svirant/DonutDongle/images/11.png

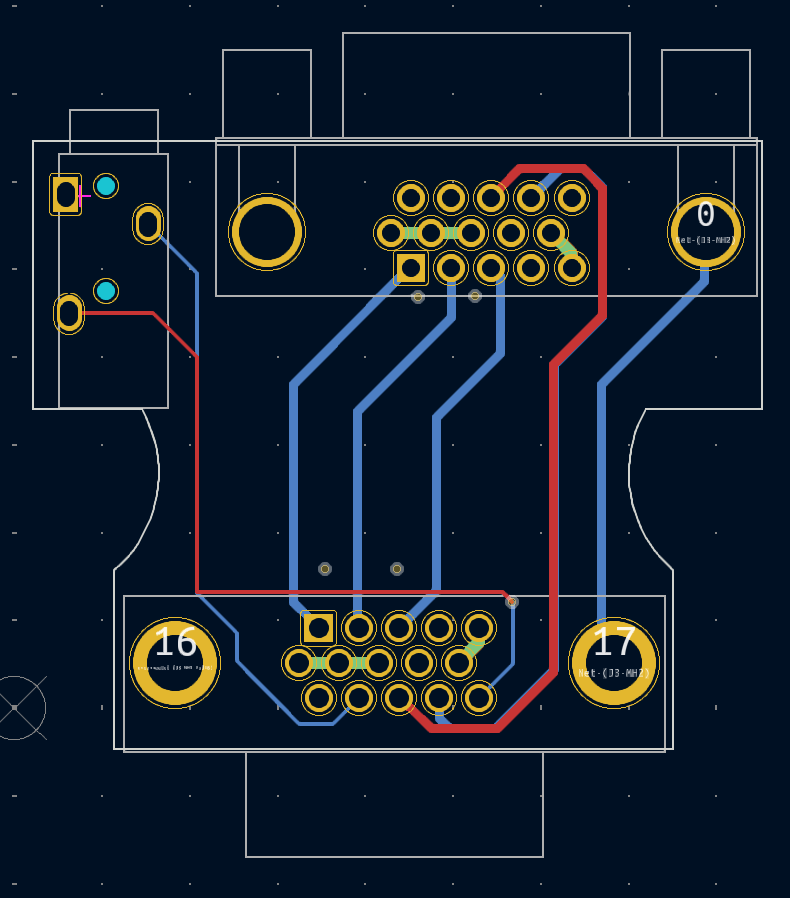
images/11.png
